SahanDissanayaka/Power-Saving-Automatic-Room-Light-Controller/Coding_part/Receiver_Side_Code/Receiver_Side_Code.ino

/// Include RadioHead Amplitude Shift Keying Library
#include <RH_ASK.h>
// Include dependant SPI Library 
#include <SPI.h> 
 
// Create Amplitude Shift Keying Object
RH_ASK rf_driver;
 
void setup()
{
    // Initialize ASK Object
    rf_driver.init();
    // Setup Serial Monitor
    Serial.begin(9600);
    pinMode(13,OUTPUT);
}
 
void loop()
{
    // Set buffer to size of expected message
    uint8_t buf[1];
    uint8_t buflen = sizeof(buf);
    // Check if received packet is correct size
    if (rf_driver.recv(buf, &buflen))
    {
      
      // Message received with valid checksum
      Serial.print("Message Received: ");
      char *data = (char *)buf;
      Serial.println(data);
      if (*data == '1'){
        digitalWrite(13,HIGH);
        }else{
          digitalWrite(13,LOW);
          }         
    }
}
